LaurinLudwig/autonomesRacingFiles/CAD/EnforcingBracket/EnforcingBracketClamp.3mf

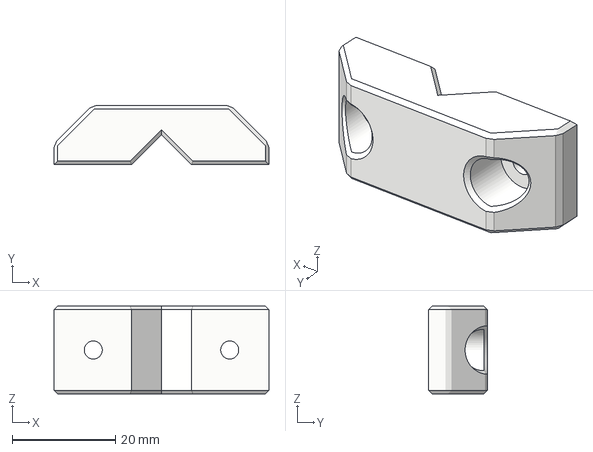
[picture p26: CAD file, 2025-11-17]
CAD/EnforcingBracket/EnforcingBracketClamp.3mf
41.6 x 11.5 x 17.0 mm
